kiwisincebirth/Floppy80-M1/firmware/file.h

#ifndef __FILE_C_
#define __FILE_C_

#ifdef __cplusplus
extern "C" {
#endif

#ifndef MFC
#include "ff.h"
#endif

#ifndef FA_READ
    #define FA_READ  0x01
    #define FA_WRITE 0x02
#endif

#define MAX_FILES 8

#ifdef MFC
    #define FIL CFile
#endif

typedef struct {
	byte byIsOpen;
	FIL  f;
} file;

/* File function return code (FRESULT) */

#ifdef MFC
typedef enum {
	FR_OK = 0,				/* (0) Succeeded */
	FR_DISK_ERR,			/* (1) A hard error occurred in the low level disk I/O layer */
	FR_INT_ERR,				/* (2) Assertion failed */
	FR_NOT_READY,			/* (3) The physical drive cannot work */
	FR_NO_FILE,				/* (4) Could not find the file */
	FR_NO_PATH,				/* (5) Could not find the path */
	FR_INVALID_NAME,		/* (6) The path name format is invalid */
	FR_DENIED,				/* (7) Access denied due to prohibited access or directory full */
	FR_EXIST,				/* (8) Access denied due to prohibited access */
	FR_INVALID_OBJECT,		/* (9) The file/directory object is invalid */
	FR_WRITE_PROTECTED,		/* (10) The physical drive is write protected */
	FR_INVALID_DRIVE,		/* (11) The logical drive number is invalid */
	FR_NOT_ENABLED,			/* (12) The volume has no work area */
	FR_NO_FILESYSTEM,		/* (13) There is no valid FAT volume */
	FR_MKFS_ABORTED,		/* (14) The f_mkfs() aborted due to any problem */
	FR_TIMEOUT,				/* (15) Could not get a grant to access the volume within defined period */
	FR_LOCKED,				/* (16) The operation is rejected according to the file sharing policy */
	FR_NOT_ENOUGH_CORE,		/* (17) LFN working buffer could not be allocated */
	FR_TOO_MANY_OPEN_FILES,	/* (18) Number of open files > FF_FS_LOCK */
	FR_INVALID_PARAMETER	/* (19) Given parameter is invalid */
} FRESULT;
#endif

//-----------------------------------------------------------------------------

file*    FileOpen(char* pszFileName, BYTE byMode);
void     FileClose(file* fp);
BYTE     FileIsOpen(file *fp);
uint32_t FileRead(file* fp, BYTE* pby, uint32_t nSize);
uint32_t FileWrite(file* fp, BYTE* pby, uint32_t nSize);
void     FileSeek(file* fp, int nOffset);
void     FileTruncate(file* fp);
void     FileFlush(file* fp);
void     FileCloseAll(void);
void     FileSystemInit(void);
int      FileReadLine(file* fp, char szLine[], int nMaxLen);
BYTE     FileExists(char* pszFileName);

#ifdef __cplusplus
}
#endif

#endif
